dchwebb/Spectralist/bu/Spectralist_Kishoof/src/Additive.h

#pragma once
#include "initialisation.h"
#include "WaveTable.h"
#include <tuple>
#include <array>

class Additive {
public:
	Additive();


	static constexpr uint32_t maxHarmonics = 200;

	//std::array<uint16_t, harmonics> readPos;
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
	uint32_t aliasHarmonic;
	float prevIncErr = 0.0f;
private:
	float FastTanh(const float x);
	inline void FilterCalc(uint32_t pos, float& scale, uint32_t& combPos, int32_t& combDir, float maxLevel);
	inline void Smooth(float& currentValue, const float newValue, const float fraction);

	float outputSamples[2] = {0.0f, 0.0f};		// Preprepared samples sent to DAC on interrupt
	float smoothedInc = 0.0f;
	static constexpr float scaleOutput = -std::pow(2.0f, 31.0f);	// Multiple to convert -1.0 - 1.0 float to 32 bit int and invert
	static constexpr float scaleVCAOutput = scaleOutput / 65536.0f;	// To scale when VCA is used
	//GpioPin octaveDown	{GPIOD, 6, GpioPin::Type::Input};
	//GpioPin debug1		{GPIOC, 10, GpioPin::Type::Output};

	float filterStart[2] = {0.0f, 0.0f};
	float filterSlope = 0.0f;
	//float startLevel = 0.0f;
	float multSpread = 0.0f;
	float multGrow = 0.0f;

	enum class Filter {LP, HP, BP, Comb, count} filterType = Filter::LP;

	int32_t filterTypeVal = 0;					// Used for setting hysteresis on filter type


	float multipliers[maxHarmonics];
};

extern Additive additive;
