dchwebb/Spectralist/bu/Spectralist_Kishoof/src/interrupts.h

void OTG_HS_IRQHandler(void) {
	usb.InterruptHandler();
}

uint32_t underrun = 0;

void SPI2_IRQHandler()
{
	// I2S Interrupt
	if ((SPI2->SR & SPI_SR_UDR) == SPI_SR_UDR) {		// Check for Underrun condition
		SPI2->IFCR |= SPI_IFCR_UDRC;					// Clear underrun condition
		++underrun;
	}

	if (modeSpectralist) {
		additive.CalcSample();
	} else {
		wavetable.CalcSample();
	}
}


void MDMA_IRQHandler()
{
	// fires when MDMA blanking graphics memory has completed
	if (MDMA->GISR0 & MDMA_GISR0_GIF0) {
		MDMA_Channel0->CIFCR |= MDMA_CIFCR_CBTIF;		// Clear transfer complete interrupt flag
		ui.bufferClear = true;
	}
}

// System interrupts
void NMI_Handler(void) {}

void HardFault_Handler(void) {
	while (1) {}
}
void MemManage_Handler(void) {
	while (1) {}
}
void BusFault_Handler(void) {
	while (1) {}
}
void UsageFault_Handler(void) {
	while (1) {}
}

void SVC_Handler(void) {}

void DebugMon_Handler(void) {}

void PendSV_Handler(void) {}

void SysTick_Handler(void) {
	++SysTickVal;
}

/*
// USART Decoder
void USART3_IRQHandler() {
	//if ((USART3->ISR & USART_ISR_RXNE_RXFNE) != 0 && !uartCmdRdy) {
	if (!uartCmdRdy) {
		uartCmd[uartCmdPos] = USART3->RDR; 				// accessing RDR automatically resets the receive flag
		if (uartCmd[uartCmdPos] == 10) {
			uartCmdRdy = true;
			uartCmdPos = 0;
		} else {
			uartCmdPos++;
		}
	}
}*/
